projectswnimee/RescueMesh/test_codes/Code_1.3.3_Node_Product_Firmware/Code_1.3.3_Node_Product_Firmware.ino

/* ============================================================
   Code 1.3.3 : Emergency Button (Node) Product Firmware
   FINAL – Wake-on-Radio FIXED
   Board  : NodeMCU ESP32 CH340 (ESP-WROOM-32)
   Module : AS32-TTL-100

   REQUIRES SHARED CONFIG:
   OPTION = 0x58 (WakeTime = 1000 ms)

   ============================================================ */

#include <Arduino.h>
#include "BluetoothSerial.h"

/* ================= PINOUT (SHARED – DO NOT CHANGE) =================
   ESP32 PIN   →  AS32 PIN
   D17 (GPIO17) → RXD
   D16 (GPIO16) → TXD
   D25 (GPIO25) → MD0
   D26 (GPIO26) → MD1
   ================================================================= */

#define LORA_TX   17   // D17 → AS32 RXD
#define LORA_RX   16   // D16 → AS32 TXD
#define LORA_MD0  25   // D25 → MD0
#define LORA_MD1  26   // D26 → MD1

HardwareSerial LoRaSerial(2);
BluetoothSerial SerialBT;

/* ================= NODE CONFIG ================= */
const String NODE_NUMBER = "Node01";   // CHANGE PER NODE
uint8_t seqCounter = 1;
const int DEFAULT_TTL = 10;

/* ================= BUFFERS ================= */
String rxBuffer = "";

/* ================= DEDUP STORAGE ================= */
String dedupList[10];
uint8_t dedupIndex = 0;

/* ================= MODE CONTROL ================= */

// Power-Saving Mode (MD0=0, MD1=1)
void setPowerSavingMode() {
  digitalWrite(LORA_MD0, LOW);   // MD0 = 0
  digitalWrite(LORA_MD1, HIGH);  // MD1 = 1
  delay(5);
  Serial.println("Entered Power Saving Mode...");
}

// Wake-Up Mode (MD0=1, MD1=0)
void setWakeUpMode() {
  digitalWrite(LORA_MD0, HIGH);  // MD0 = 1
  digitalWrite(LORA_MD1, LOW);   // MD1 = 0
  delay(20); 
  Serial.println("Entered Wake Up Mode...");                    // REQUIRED mode settle time
}

/* ================= DEDUP FUNCTIONS ================= */

bool isDuplicate(String id) {
  for (int i = 0; i < 10; i++) {
    if (dedupList[i] == id) return true;
  }
  return false;
}

void storeDedupID(String id) {
  dedupList[dedupIndex] = id;
  dedupIndex = (dedupIndex + 1) % 10;
}

/* ================= TRANSMIT FUNCTION ================= */

void transmitWakeupMessage(String payload) {

  String seqStr = (seqCounter < 10) ? "0" + String(seqCounter) : String(seqCounter);
  seqCounter++;

  String fullMsg =
    NODE_NUMBER + "|" +
    seqStr + "|" +
    String(DEFAULT_TTL) + "|" +
    payload + "\n";

  setWakeUpMode();   // 🔑 adds wake-up code (hardware)
  LoRaSerial.write(fullMsg.c_str(), fullMsg.length());
  delay(10);         // allow TX FIFO flush
  setPowerSavingMode();

  Serial.print("[Wake-TX] ");
  Serial.print(fullMsg);
}

/* ================= SETUP ================= */

void setup() {
  Serial.begin(115200);
  delay(1000);

  pinMode(LORA_MD0, OUTPUT);
  pinMode(LORA_MD1, OUTPUT);

  LoRaSerial.begin(9600, SERIAL_8N1, LORA_RX, LORA_TX);
  SerialBT.begin("ESP32_BT_MONITOR");

  randomSeed(micros());

  setPowerSavingMode();   // default sleep-monitor mode

  Serial.println("=== Code 1.3.3 : Emergency Node (Wake-on-Radio FINAL FIXED) ===");
}

/* ================= LOOP ================= */

void loop() {

  /* ============================================================
     LAPTOP SERIAL → WAKE-UP TRANSMIT (TEST)
     ============================================================ */
  if (Serial.available()) {
    String msg = Serial.readStringUntil('\n');
    msg.trim();
    if (msg.length()) transmitWakeupMessage(msg);
  }

  /* ============================================================
     BLUETOOTH → WAKE-UP TRANSMIT (PRODUCT PATH)
     ============================================================ */
  if (SerialBT.available()) {
    String btMsg = SerialBT.readStringUntil('\n');
    btMsg.trim();
    if (btMsg.length()) transmitWakeupMessage(btMsg);
  }

  /* ============================================================
     LORA RECEIVE + TTL + DEDUP + RANDOM DELAY + REBROADCAST
     ============================================================ */
  while (LoRaSerial.available()) {
    char c = LoRaSerial.read();

    if (c == '\n') {

      Serial.print("[Received] ");
      Serial.println(rxBuffer);

      int p1 = rxBuffer.indexOf('|');
      int p2 = rxBuffer.indexOf('|', p1 + 1);
      int p3 = rxBuffer.indexOf('|', p2 + 1);

      if (p1 > 0 && p2 > p1 && p3 > p2) {

        String nodeNo = rxBuffer.substring(0, p1);
        String seqNo  = rxBuffer.substring(p1 + 1, p2);
        int ttl       = rxBuffer.substring(p2 + 1, p3).toInt();
        String msg    = rxBuffer.substring(p3 + 1);

        if (ttl <= 0) {
          Serial.println("[Dropped] TTL expired");
          rxBuffer = "";
          return;
        }

        String dedupID = nodeNo + seqNo;
        if (isDuplicate(dedupID)) {
          Serial.println("[Dropped] Duplicate");
          rxBuffer = "";
          return;
        }

        storeDedupID(dedupID);

        int randomDelayMs = random(1000, 5001);
        Serial.print("[Rebroadcast Delay] ");
        Serial.print(randomDelayMs);
        Serial.println(" ms");
        delay(randomDelayMs);

        setWakeUpMode();

        String rebroadcastMsg =
          nodeNo + "|" +
          seqNo + "|" +
          String(ttl - 1) + "|" +
          msg + "\n";

        LoRaSerial.write(rebroadcastMsg.c_str(), rebroadcastMsg.length());
        delay(10);
        setPowerSavingMode();

        Serial.print("[Rebroadcasted] ");
        Serial.print(rebroadcastMsg);
      }

      rxBuffer = "";
    } else {
      rxBuffer += c;
    }
  }
}
