projectswnimee/RescueMesh/test_codes/Code_1.3.2.1_Gateway_Backend_Upload_Test/Reciever_Code/secrets.example.h

#pragma once
// Copy this file to secrets.h. That local file is excluded from Git.
#define WIFI_SSID "YOUR_LAB_WIFI_SSID"
#define WIFI_PASSWORD "YOUR_LAB_WIFI_PASSWORD"
#define WEBHOOK_URL "https://example.com/your-test-endpoint"
